adriangalera/galitas32/experiments/minimal.cpp

#include <Arduino.h>

void setup() {
    Serial.begin(115200);
    delay(1000);

    Serial.println("===== APPLICATION STARTED =====");
}

void loop() {
    Serial.println("alive");
    delay(1000);
}
